robotics-and-innovation-club/WRO2022-Future-Engineer/schemes/diagram_fritzing.png

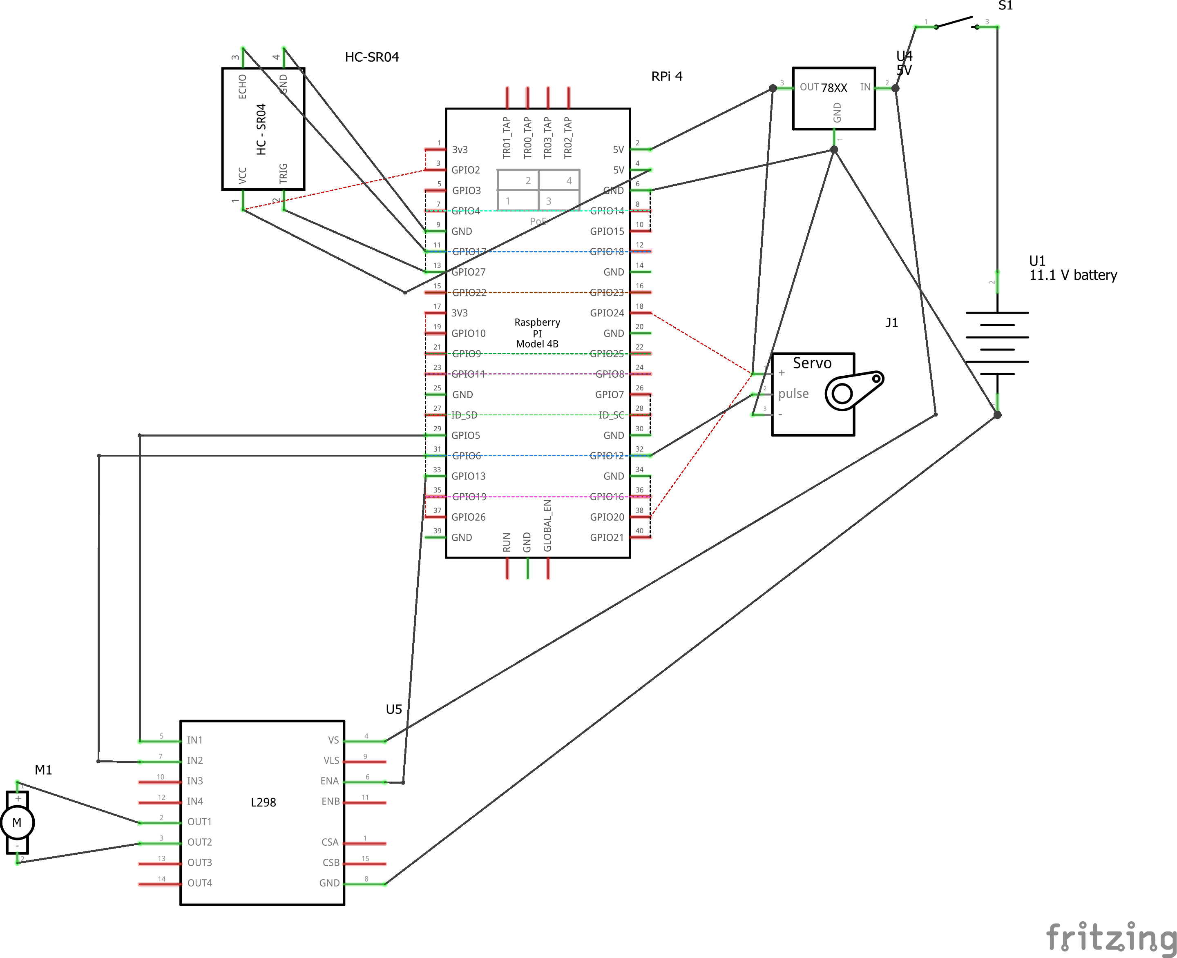
schemes/diagram_fritzing.png
