robotics-and-innovation-club/WRO2022-Future-Engineer/team-photos/Official Photo.jpg

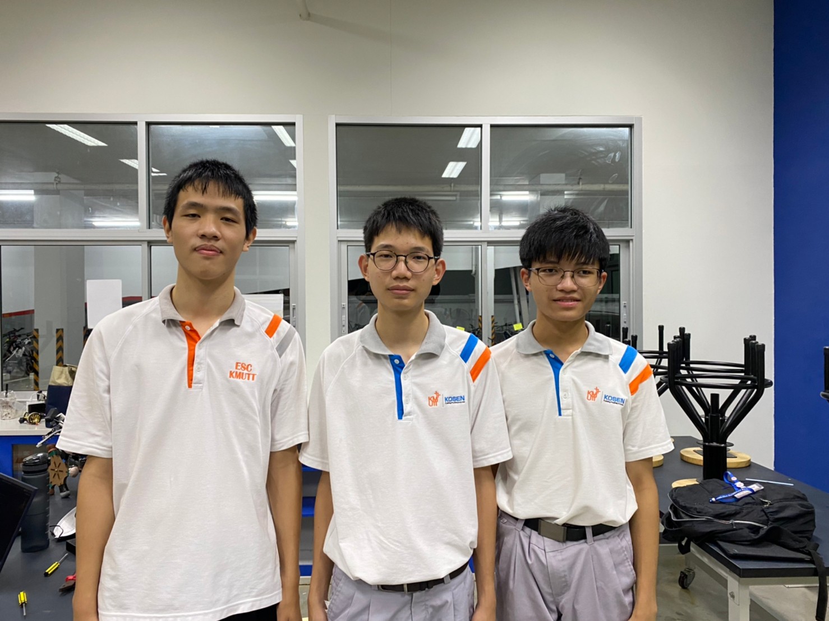
team-photos/Official Photo.jpg
