robotics-and-innovation-club/WRO2022-Future-Engineer/vehicle-photos/BACK.jpg

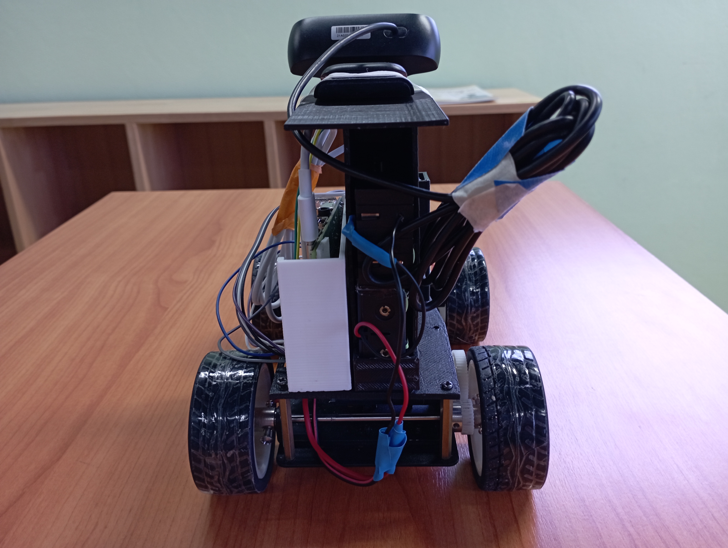
vehicle-photos/BACK.jpg
